fayekdev/HackPad/Code/Software.devPAD/backend/layout.py

"""

(x_center, y_center, width, height)

"""

HITBOXES = {

    # ----------------------------
    # Main controls
    # ----------------------------

    "display": (
        0.50,
        0.25,
        0.42,
        0.20
    ),

    "encoder": (
        0.83,
        0.32,
        0.06,
        0.08
    ),

    "joystick": (
        0.50,
        0.70,
        0.15,
        0.15
    ),

    "menu": (
        0.96,
        0.06,
        0.05,
        0.05
    ),

    # ----------------------------
    # Left Side
    # ----------------------------

    "key_1": (0.25, 0.52, 0.08, 0.10),
    "key_2": (0.35, 0.52, 0.08, 0.10),

    "key_3": (0.22, 0.70, 0.08, 0.10),
    "key_4": (0.32, 0.70, 0.08, 0.10),

    "key_5": (0.17, 0.86, 0.08, 0.10),
    "key_6": (0.27, 0.86, 0.08, 0.10),
    "key_7": (0.38, 0.86, 0.08, 0.10),

    # ----------------------------
    # Right Side
    # ----------------------------

    "key_8": (0.65, 0.52, 0.08, 0.10),
    "key_9": (0.75, 0.52, 0.08, 0.10),

    "key_10": (0.68, 0.70, 0.08, 0.10),
    "key_11": (0.78, 0.70, 0.08, 0.10),

    "key_12": (0.63, 0.86, 0.08, 0.10),
    "key_13": (0.73, 0.86, 0.08, 0.10),
    "key_14": (0.83, 0.86, 0.08, 0.10)
}
